Bach-Nguyen-Dinh/Macro-SEL-Detection-and-Recovery/MacroSEL_v4_Complete.docx

Macro-SEL Protection System

Version 0.1

Radiation-Tolerant Latch-up Detection and Recovery

Edge Computer for LEO Orbit

3-Year Minimum Mission Requirement

February 2026

Table of Contents

# Part 1: Macro-SEL Protection Design Overview

## 1. Introduction

This document describes the Macro-SEL (macro single-event latch-up) protection system for a space-qualified edge computer designed for Low Earth Orbit (LEO) missions with a minimum 3-year operational requirement.

The system protects ARM Cortex-A72 CPUs, AI cores, DDR4 RAM, and eMMC storage built on advanced process nodes using commercial off-the-shelf (COTS) components rather than radiation-hardened alternatives.

### 1.1 Major Improvements in v4.0

Version 4.0 represents a fundamental redesign with significant architectural improvements:

• Op-amp upgrade: OPA4H838-SEP with 5V supply capability, 10 MHz GBW (4× faster than v3.3)

• Single 5V power domain: All circuits powered from 5V_IN (eliminates split-domain complexity)

• 10ms blanking window: Properly masks inrush current AFTER FET turn-on

• Response time improvement: 10.1µs → 3.9µs worst case (2.6× faster)

## 2. System Architecture

### 2.1 Protection Strategy

The system employs a hardware-only autonomous protection approach:

• One master P-channel MOSFET (high-side, 5V input rail)

• Six independent current-sensing channels (one per downstream rail)

• Wired-AND comparator bus (any fault triggers global fault)

• Hardware-only infinite retry: ~1 second off between attempts

• 10ms blanking window after FET turn-on (masks inrush)

• SR latch maintains fault state during power loss

### 2.2 Response Time Performance

Rail | Voltage | Current | Gain | Amplifier Time | Total Response
1 | 3.3V | 5A | 13.18× | 0.46 µs | 1.61 µs
2 | 3.3V | 5A | 13.18× | 0.46 µs | 1.61 µs
3 | 1.2V | 3A | 21.90× | 0.77 µs | 1.92 µs
4 | 1.35V | 0.4A | 32.90× | 1.15 µs | 2.30 µs
5 | 1.8V | 2A | 32.90× | 1.15 µs | 2.30 µs
6 | 2.5V | 1A | 65.89× | 2.30 µs | 3.45 µs

All response times are well within the safe window for macro-SEL protection (10-1000 µs), providing 3× to 300× safety margin.

## 3. Power Budget

### 3.1 Input Power

5V @ 5A maximum from spacecraft bus (25W total system budget)

### 3.2 Protected Rails

Rail | Voltage | Current | Load | Shunt | Trip Threshold
1 | 3.3V | 5A | AI Core 1 | 10 mΩ | 7.5A (150%)
2 | 3.3V | 5A | AI Core 2 | 10 mΩ | 7.5A (150%)
3 | 1.2V | 3A | CPU + DDR4 | 10 mΩ | 4.5A (150%)
4 | 1.35V | 0.4A | CPU | 50 mΩ | 0.6A (150%)
5 | 1.8V | 2A | CPU + eMMC | 10 mΩ | 3.0A (150%)
6 | 2.5V | 1A | CPU + DDR4 | 10 mΩ | 1.5A (150%)

Note: Rail 4 uses 50mΩ shunt (v4.0 change) to reduce voltage drop from 40mV to 20mV, saving critical margin for 1.35V rail.

### 3.3 Protection Circuit Power Consumption

All protection circuits powered from 5V_IN (single power domain):

• 2× OPA4H838-SEP op-amps: 5.2 mA

• 2× TLV1704-SEP comparators: 0.3 mA

• 5× Logic ICs (SN54SC series): 0.1 mA

• V_ref dividers (5 total): 0.5 mA

• Wired-AND pull-up resistor: 0.5 mA

• Total: ~6.6 mA @ 5V = 33 mW (0.13% of system budget)

## 4. Major Components

### 4.1 Master Protection Switch

Q1: BUP06CP038F-01 P-channel MOSFET

• Package: DPAK (TO-252AA)

• V_DSS: -55V

• I_D: -35A continuous, -140A pulsed

• R_DS(on): 38 mΩ typ @ Vgs = -4.5V

• TID: 30-50 krad(Si)

• SEE LET: 46 MeV·cm²/mg

### 4.2 Op-Amps

U_AMP_A, U_AMP_B: OPA4H838-SEP (quad op-amp)

• Package: CFP-14 hermetic flatpack

• Supply: 2.5V - 5.5V (powered at 5V from 5V_IN)

• GBW: 10 MHz (4× improvement over LMP7704-SP)

• Slew rate: 5 V/µs (5× improvement)

• Input offset: ±2.25 µV (200× better than LMP7704-SP)

• Offset drift: ±0.005 µV/°C (zero-drift technology)

• Input CM range: -0.1V to 5.1V (excellent headroom for 3.3V rails)

• TID: 30 krad(Si) RLAT

• SEE LET: 43 MeV·cm²/mg

### 4.3 Comparators

U_CMP_A, U_CMP_B: TLV1704-SEP (quad comparator)

• Package: TSSOP-14

• Supply: 2.2V - 24V (powered at 5V from 5V_IN)

• Propagation delay: 560 ns typical

• Output type: Open-drain (critical for wired-AND operation)

• TID: 30 krad(Si) RLAT

• SEE LET: 43 MeV·cm²/mg

## 5. Wired-AND Architecture

The design employs a critical architectural simplification using open-drain comparator outputs in a wired-AND configuration.

### 5.1 Principle of Operation

All six comparator outputs are tied together to a single bus wire with one 10kΩ pull-up resistor to 5V. This creates an inherent AND function:

• When ALL comparators are Hi-Z (no faults): Bus pulled HIGH by resistor → GLOBAL_FAULT_n = HIGH

• When ANY comparator drives LOW (fault detected): Bus pulled to GND → GLOBAL_FAULT_n = LOW

## 6. Control Logic

### 6.1 Blanking Window (10ms Inrush Masking)

A critical feature to properly handle Buck #1 input capacitor charging inrush:

• Triggered by ENABLE_GLOBAL rising edge (when FET turns ON)

• Duration: 9.5ms - 15.5ms (RC timing with component variation)

• Implementation: 10nF capacitor + 1MΩ resistor + Schmitt trigger

• Function: Masks fault detection during inrush period

### 6.2 SR Latch (Fault State Memory)

Remembers fault occurrence even after rails collapse to 0V:

• IC: SN54SC4T00-SEP (quad 2-input NAND)

• Active-LOW inputs: SET_L and RESET_L

• Output: FAULT_LATCHED (HIGH = fault remembered)

• Critical function: Prevents immediate restart when rails collapse

### 6.3 Retry Timer

Holds system off for ~1 second after fault shutdown:

• RC circuit: 1.0MΩ + 2.2µF

• Delay range: 0.7s - 1.7s (component variation)

• Discharge transistor: Q_dis (JANTXV2N2222A NPN)

• Controlled by FAULT_LATCHED output

### 6.4 Enable Logic

Matches logic coming out of the latch to the logic driving P-MOSFET gate

• Just one inverter gate

## 7. Bill of Materials Summary

### 7.1 Active Components (9 ICs total)

Component | Part Number | Function | Qty
Q1 | BUP06CP038F-01 | Master P-FET | 1
U_AMP | OPA4H838-SEP | Quad op-amp | 2
U_CMP | TLV1704-SEP | Quad comparator | 2
U_LATCH | SN54SC4T00-SEP | Quad NAND (latch) | 1
U_OR | SN54SC4T32-SEP | Dual OR (blanking) | 1
U_SCH | SN54SC6T17-SEP | Hex Schmitt buffer | 1
U_INV | SN54SC6T14-SEP | Hex Schmitt inverter | 1
Q_dis | JANTXV2N2222A | NPN transistor | 1

# Part 2: Complete Single Rail Diagram - Rail 1

## 9. Rail 1 Overview

This section provides a complete detailed diagram for Rail 1 (3.3V / 5A, AI Core 1), showing the entire signal path from power input to the P-FET gate driver.

Rail 1 specifications:

• Voltage: 3.3V

• Rated current: 5A

• Load: AI Core 1

• Shunt resistor: 10 mΩ (WSL2512R0100FEA)

• Trip threshold: 7.5A (150% of rated)

• Op-amp gain: 13.18×

• Response time: 1.61 µs (fastest rail)

## 10. Current Sensing Stage

### 10.1 Shunt Resistor

The shunt resistor converts rail current into a measurable voltage drop:

Buck #1 R_S1 AI Core 1

Output (Shunt) Load

3.3V 10mΩ 5A max

│ │ │

├───[====]──┤ │

│ WSL │ │

│ 2512 │ │

V_RAIL+ V_RAIL- 3.3V_LOAD

(sense+) (sense-)

Component: WSL2512R0100FEA (Vishay Dale)

• Resistance: 10 mΩ ± 1%

• Power rating: 2W

• Package: 2512 SMD with 4-wire Kelvin connection

Voltage drops:

• Normal (5A): V_drop = 5A × 10mΩ = 50mV (1.5% of 3.3V rail)

• Trip threshold (7.5A): V_drop = 7.5A × 10mΩ = 75mV

### 10.2 Difference Amplifier

4-resistor instrumentation amplifier topology converts small differential voltage into larger single-ended signal:

V_RAIL+ V_RAIL-

(3.3V) (3.3V - 50mV)

│ │

[R_p1] [R_p2]

1kΩ 1kΩ

│ │

├────[R1]────┐ ┌────[R3]────┤

│ 9.09kΩ │ │ 9.09kΩ │

│ │ │ │

│ ┌──▼──────────────▼──┐ │

│ │ OPA4H838-SEP │ │

│ │ (Channel A) │ │

│ │ │ │

└─[R2]───│ │───[R4]──┘

133kΩ │ │ 133kΩ

└─────── V_AMP_1 ────┘

Component values:

• R_p1, R_p2: 1.0 kΩ (input protection, limits current if differential exceeds ±0.2V)

• R1, R3: 9.09 kΩ (0.1% tolerance, E96 series)

• R2, R4: 133 kΩ (0.1% tolerance, E96 series)

Gain calculation:

• Effective R1 = 9.09kΩ + 1.0kΩ = 10.09kΩ

• Gain = R2 / R1_eff = 133kΩ / 10.09kΩ = 13.18×

Signal levels:

• Normal (5A): V_sense = 50mV → V_AMP_1 = 659mV

• Trip (7.5A): V_sense = 75mV → V_AMP_1 = 988mV

• Fault (20A): V_AMP_1 saturates at ~2.2V (op-amp output limit)

Bandwidth and response time:

• GBW = 10 MHz (OPA4H838-SEP)

• BW = GBW / Gain = 10 MHz / 13.18 = 759 kHz

• t_rise = 0.35 / BW = 0.46 µs (4× faster than LMP7704-SP!)

## 11. Voltage Reference Generation

V_ref provides the threshold voltage for fault detection. Target is ~1.0V to match V_AMP at 150% current.

NOTE: Rails 1 & 2 share ONE V_ref divider (both are 3.3V/5A with identical trip points).

5V_IN (always present)

│

[R_top]

40.2kΩ

│

├───────┬──────> V_ref = 0.996V

│ │

[R_bot] [C_ref]

10.0kΩ 100nF

│ │

├───────┘

GND

Calculation:

• V_ref = 10.0kΩ / (40.2kΩ + 10.0kΩ) × 5V = 0.996V

• Error from 1.0V target: 0.4% (excellent accuracy)

Tolerance analysis:

• Resistor tolerance: ±0.1% (E96 precision)

• Worst case range: 0.994V - 0.998V (±0.2% variation)

• Temperature coefficient: ±9mV over -55°C to +125°C range

## 12. Comparator Stage

TLV1704-SEP comparator with open-drain output detects when amplified signal exceeds threshold:

V_ref ─────────┐

0.996V │

└────────────>│ IN+ (pin 3)

│

V_AMP_1 ───────────────────>│ IN- (pin 2)

(from op-amp) │

│ TLV1704-SEP

│ Comparator #1

│

│ OUT (pin 1)

└──────> To WIRED-AND BUS

Comparator logic:

• IN+ = V_ref = 0.996V (fixed reference)

• IN- = V_AMP_1 (variable, tracks rail current)

Operation:

• Normal: V_AMP_1 < V_ref → IN+ > IN- → Output Hi-Z

• Fault: V_AMP_1 > V_ref → IN+ < IN- → Output drives LOW

Voltage comparison examples:

Load Current | V_AMP_1 | Comparison | Output State | Status
5A (100%) | 659mV | 659mV < 996mV | Hi-Z | Normal
7A (140%) | 922mV | 922mV < 996mV | Hi-Z | Normal
7.6A (152%) | 1002mV | 1002mV > 996mV | LOW | FAULT!
15A (300%) | 2200mV | 2200mV > 996mV | LOW | FAULT!

## 13. Wired-AND Bus

All 6 comparator outputs tied together with single 10kΩ pull-up resistor:

From Rail 1 From Rail 2 From Rail 3

Comparator Comparator Comparator

│ │ │

└───────┬───────┴───────┬───────┴─── ... (Rails 4-6)

│ │ │

└───────────────┴───────────────┘

│

│ WIRED-AND BUS

[R_pull: 10kΩ]

│

5V_IN

│

▼

GLOBAL_FAULT_n

Bus signal states:

• ALL rails normal (all 6 comparators Hi-Z): Bus = HIGH (~5V)

• Rail 1 faults (comparator 1 drives LOW): Bus = LOW (~0V)

• Multiple rails fault: All share pull-down current, bus = LOW

• During shutdown (all V_AMP = 0V): Comparators Hi-Z, bus = HIGH (false indication, but SR latch remembers fault)

## 14. Blanking Gate

OR gate combines fault signal with blanking timer to mask faults during Buck #1 inrush:

GLOBAL_FAULT_n ────┐

(from wired-AND) │

┌──▼──┐

BLANKING ───────┤ │ SN54SC4T32-SEP

(from timer) │ OR │ (U_OR, gate #1)

│ │

└──┬──┘

│

▼

SET_L

(to SR latch)

Truth table:

GLOBAL_FAULT_n | BLANKING | SET_L | Meaning
HIGH | HIGH | HIGH | Startup: faults masked
HIGH | LOW | HIGH | Normal: no fault
LOW | HIGH | HIGH | Inrush fault: MASKED!
LOW | LOW | LOW | Real fault: trigger latch

Critical function: During 10ms blanking window, even if inrush triggers GLOBAL_FAULT_n = LOW, the OR gate keeps SET_L = HIGH (inactive), preventing false shutdown.

## 15. Blanking Timer

Generates 10ms HIGH pulse starting when ENABLE_GLOBAL rises (FET turns ON):

ENABLE_GLOBAL ──┬─────[C_blank]─────┬──── BLANK_NODE

│ 10nF │

│ [R_blank]

│ 1.0MΩ

│ │

│ GND

│

│ ┌────────┐

│ │Schmitt │ SN54SC6T17-SEP

│ │Trigger │ (U_SCH, gate #1)

│ └────┬───┘

│ │

│ ▼

│ BLANKING

Operation sequence:

1. FET OFF: BLANK_NODE = 0V, BLANKING = LOW

2. ENABLE_GLOBAL rises: Rising edge couples through C_blank

3. BLANK_NODE spikes HIGH (~3.5V), BLANKING = HIGH

4. Next 10ms: C_blank discharges through R_blank exponentially

5. After ~10ms: BLANK_NODE drops below threshold, BLANKING = LOW

Timing:

• RC = 1.0MΩ × 10nF = 10ms time constant

• Blanking duration: 9.5ms - 15.5ms (Schmitt threshold variation)

• Masks Buck #1 inrush current (typically 2-5ms duration)

## 16. SR Latch

Cross-coupled NAND gates remember fault state during power loss:

┌──────┐

SET_L ────┤ │

│ NAND ├────┬──→ Q (FAULT_LATCHED)

┌────┤ │ │

│ └──────┘ │

│ │

│ ┌──────┐ │

└────┤ │ │

│ NAND ├────┘

RESET_L ──┤ │

└──────┘

IC: SN54SC4T00-SEP (quad 2-input NAND), uses gates 1 and 2

Operation states:

SET_L | RESET_L | Action | FAULT_LATCHED
HIGH | HIGH | Hold (no change) | Previous state
LOW | HIGH | SET (latch fault) | HIGH
HIGH | LOW | RESET (clear fault) | LOW
LOW | LOW | Invalid (avoid) | Undefined

Critical function: When rails collapse to 0V, GLOBAL_FAULT_n goes HIGH but latch HOLDS FAULT_LATCHED = HIGH, keeping system off until retry timer resets it.

## 17. Retry Timer

Holds system off for ~1 second after fault shutdown:

5V_IN ───[R_timer]─── TIMING_B ───[C_timer]─── GND

1.0MΩ │ 2.2µF

│

│ Q_dis

│ (JANTXV2N2222A)

│ │

└─────> Collector

Emitter → GND

Base ←[10kΩ]← INV(FAULT_LATCHED)

TIMING_B ────┐

│

┌───▼───┐

│Schmitt│ SN54SC6T17-SEP

│Trigger│ (U_SCH, gate #2)

└───┬───┘

│

▼

RETRY_ACTIVE

Operation:

• Normal (no fault): FAULT_LATCHED = LOW → Q_dis ON → TIMING_B = 0V

• Fault occurs: FAULT_LATCHED = HIGH → Q_dis OFF → C_timer charges

• Charging: 0.7s - 1.7s to reach Schmitt threshold

• Timer expires: RETRY_ACTIVE = HIGH → generates RETRY_PULSE

• RETRY_PULSE resets latch: FAULT_LATCHED = LOW → Q_dis ON → cap discharges

Timing calculation:

• RC = 1.0MΩ × 2.2µF = 2.2 seconds time constant

• Delay = 2.2s × ln(5V / (5V - V_threshold))

• Range: 0.72s - 1.72s depending on Schmitt threshold (1.43V - 2.71V)

## 18. Retry Pulse Generation

Converts RETRY_ACTIVE rising edge into brief pulse to reset SR latch:

RETRY_ACTIVE ────[C_pulse]──── RETRY_PULSE ────[R_pull]──── GND

10nF │ 100kΩ

│

▼

To RESET_L input

(via inverter)

Operation:

• RETRY_ACTIVE LOW: RETRY_PULSE = 0V

• RETRY_ACTIVE rises: Rising edge couples through capacitor → RETRY_PULSE spikes HIGH

• Next 5ms: C_pulse discharges through R_pull → RETRY_PULSE decays to 0V

• Pulse width: ~5ms (much longer than needed for latch reset)

Inversion:

• RETRY_PULSE (HIGH pulse) → Inverter gate #3 → RESET_L (LOW pulse)

• SR latch sees LOW on RESET_L → resets to FAULT_LATCHED = LOW

## 19. Enable Logic

Simplified in v4.0 to just one inverter:

FAULT_LATCHED ────┤►├──── ENABLE_GLOBAL

Inverter (to gate driver)

(U_INV #4)

Logic:

FAULT_LATCHED | ENABLE_GLOBAL | P-FET State
LOW (no fault) | HIGH | ON
HIGH (fault) | LOW | OFF

Why so simple?

• Blanking window handles inrush masking AFTER FET turns on

• No need for complex startup delay logic

• First retry timer delay (~1s) serves as startup delay on power-up

## 20. P-FET Gate Driver

Inverts ENABLE_GLOBAL and drives P-channel MOSFET gate:

ENABLE_GLOBAL ────┤►├──── GATE_DRIVE

Inverter (to P-FET gate)

(U_INV #1)

5V_IN ──┬───[R1: 10kΩ]──┬─── GATE (Q1)

│ │

│ ├───[R2: 100Ω]─── GATE_DRIVE

│ │

│ [C2: 100nF]

│ │

┌───┴────────────────┴───┐

│ BUP06CP038F-01 │

│ P-Channel MOSFET │

│ │

│ Source (S) = 5V_IN │

│ Drain (D) = 5V_OUT │

└────────────────────────┘

Gate driver logic:

• ENABLE_GLOBAL = HIGH: GATE_DRIVE = LOW → Vgs = -5V → FET ON

• ENABLE_GLOBAL = LOW: GATE_DRIVE = HIGH → Vgs = 0V → FET OFF

Gate circuit components:

• R1 (10kΩ): Pull-up to 5V, ensures fail-safe OFF if driver loses power

• R2 (100Ω): Series resistor limits gate current, controls dV/dt

• C2 (100nF): Gate-to-source snubber reduces ringing

Switching timing:

• Gate RC: τ = 100Ω × 2.5nF (C_GS) = 250ns

• Turn-on time: ~500ns (3× time constant)

• Turn-off time: ~500ns

## 21. Complete Timing Analysis - Rail 1 Fault Event

Timeline from cosmic ray strike to system shutdown:

Time | Event | Signal State
T = 0 µs | Cosmic ray strikes AI Core 1 | Normal operation
T = 0-5 µs | Latch-up current builds: 5A → 20A | V_sense: 50mV → 200mV
T = 0.46 µs | Op-amp responds (63% rise) | V_AMP_1 rising
T = 2 µs | V_AMP_1 crosses threshold | V_AMP_1 = 1.5V > V_ref
T = 2.6 µs | Comparator detects fault | OUT goes LOW
T = 2.61 µs | Wired-AND bus updates | GLOBAL_FAULT_n = LOW
T = 2.62 µs | Blanking gate (not blanking) | SET_L = LOW
T = 2.63 µs | SR latch SETS | FAULT_LATCHED = HIGH
T = 2.64 µs | Enable logic updates | ENABLE_GLOBAL = LOW
T = 3 µs | P-FET turning OFF | Gate rising
T = 3.5 µs | P-FET fully OFF | 5V_OUT collapses
T = 4 µs | Rail 1 voltage dropping | Latch-up extinguishing
T = 10 ms | All rails at 0V | Latch-up fully stopped

Total response time: 1.61 µs (fault detection to FET off)

Margin vs macro-SEL: 6× to 600× safety factor

## 22. Inverter Usage Summary

One hex inverter IC (U_INV: SN54SC6T14-SEP Schmitt inverter) provides all inversion functions:

Gate | Input | Output | Purpose
#1 | ENABLE_GLOBAL | GATE_DRIVE | P-FET gate driver

#2 | FAULT_LATCHED | Q_dis control | Timer discharge control

#3 | RETRY_PULSE | RESET_L | Latch reset (active-LOW)

#4 | FAULT_LATCHED | ENABLE_GLOBAL | Simple enable logic

#5 | Unused | No-connect | Tied to GND

#6 | Unused | No-connect | Tied to GND

## 23. Conclusion

This document has presented the complete Macro-SEL Protection v4.0 design, including:

• Comprehensive system architecture with major improvements over v3.3

• Single 5V power domain simplification

• Wired-AND comparator bus innovation (eliminates 2 ICs, $400 savings)

• Properly positioned 10ms blanking window for inrush masking

• Detailed single-rail diagram showing complete signal path

• Full component specifications and calculations

• Complete timing analysis demonstrating adequate response times

The system provides autonomous hardware-only protection against macro-SEL events with:

• Response time: 1.6µs - 3.5µs (well within macro-SEL safe window)

• Infinite autonomous retry capability

• Total component cost: $4,035 (16.6% reduction from v3.3)

• Component count: 9 active ICs (25% reduction from v3.3)

This design is ready for PCB layout and prototype fabrication.
